marksidell/wordclock/code/wordclock/configdefs.py

'''
Namedtuples used in the config files
'''

from collections import namedtuple

ALL_WORDS = []

class Word:
    ''' Defines a word on the clock face
    '''
    #pylint: disable=too-few-public-methods

    def __init__(self, text, y, x, vertical=False):
        '''
        text: The word text, used to calculate its length
        y:        # The starting row
        x:        # The startin column
        vertical: # True if the word is vertical
        after:    # A list of the words that appear after this word in the gripd
        poems:    # A list of poems starting with this word
        '''
        self.text = text
        self.y = y #pylint: disable=invalid-name
        self.x = x #pylint: disable=invalid-name
        self.vertical = vertical
        self.after = None
        self.poems = None

        ALL_WORDS.append(self)


# Defines a birthday
#
BirthDate = namedtuple(
    'BirthDate',
    [
        'month',    # The month (1..12)
        'day',      # The month day (1..)
    ])

# Used to cause the clock to display the birthday message on a
# special range of days. I used this when I ended up delivering the
# clock late, and wanted my not to wait a year to see the greeting.
#
SpecialBirthday = namedtuple(
    'SpecialBirthday',
    [
        'name',     # The config variable for the name to display
        'begin',    # A datetime.Date() specifying the start day
        'end',      #  A datetime.Date() specifying the day after the end day
    ])
